javacasm/microbitLovesPlants/images/DeterioroSensorHumedad1.jpg

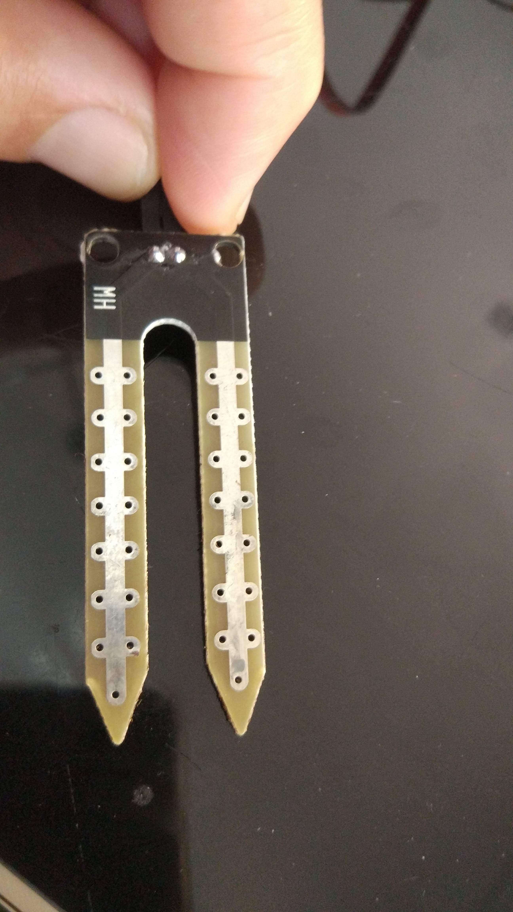
images/DeterioroSensorHumedad1.jpg
