javacasm/microbitLovesPlants/images/ModuloRele.png

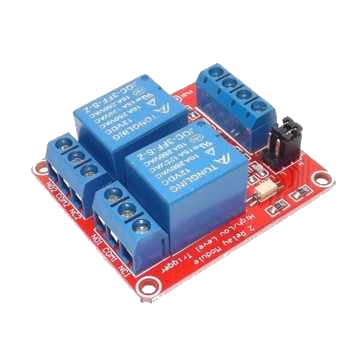
images/ModuloRele.png
